NBER08/StartrackerOrion-Hardware/HTML/images/cat_pdf_drill_map_Orion-NPTH_drill_map.png

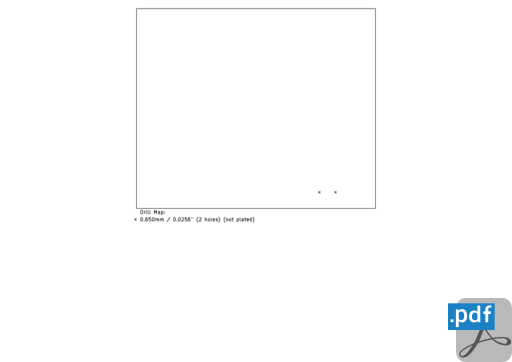
HTML/images/cat_pdf_drill_map_Orion-NPTH_drill_map.png
