NBER08/StartrackerOrion-Hardware/HTML/images/cat_pdf_drill_map_Orion-PTH_drill_map.png

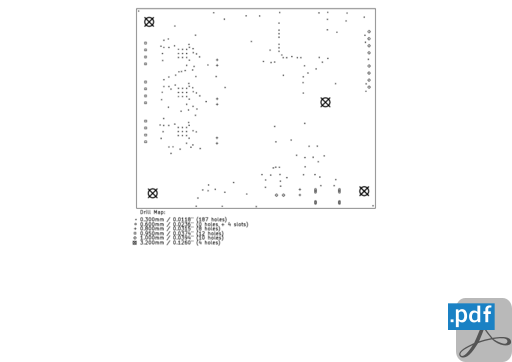
HTML/images/cat_pdf_drill_map_Orion-PTH_drill_map.png
