NBER08/StartrackerOrion-Hardware/HTML/images/cat_png_3d_viewer_bottom_Orion-bottom.png

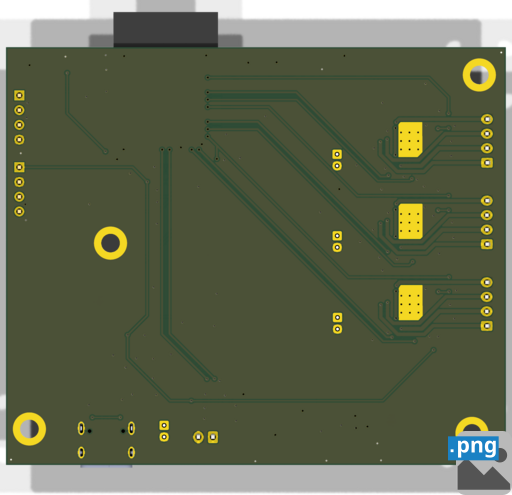
HTML/images/cat_png_3d_viewer_bottom_Orion-bottom.png
