NBER08/StartrackerOrion-Hardware/HTML/images/cat_png_3d_viewer_top_Orion-top.png

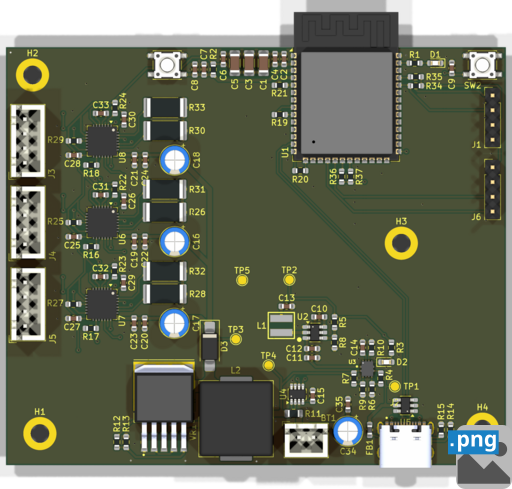
HTML/images/cat_png_3d_viewer_top_Orion-top.png
