NBER08/StartrackerOrion-Hardware/Images/Orion-bottom.png

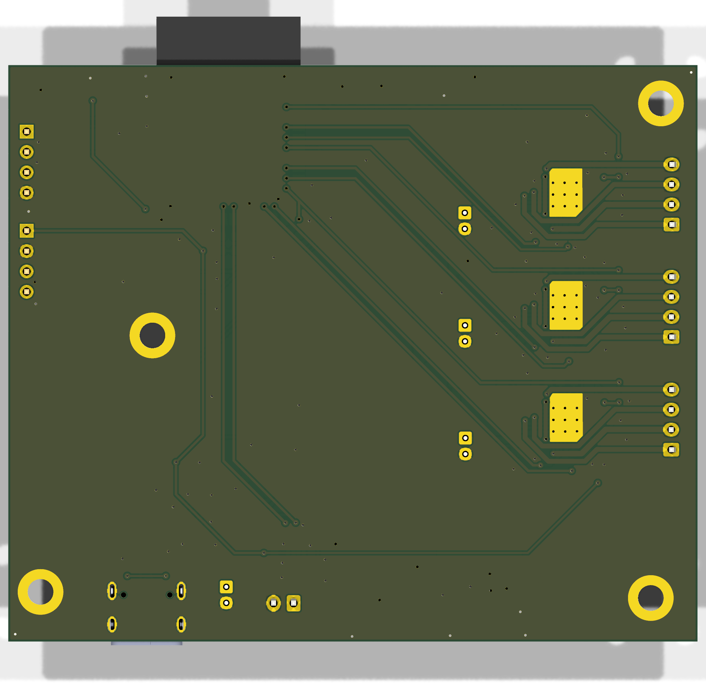
Images/Orion-bottom.png
