NBER08/StartrackerOrion-Hardware/Manufacturing/Fabrication/Orion-fabrication.pdf

# Top Fabrication (Scale 1:1)

# Orion Main Fabrication Document

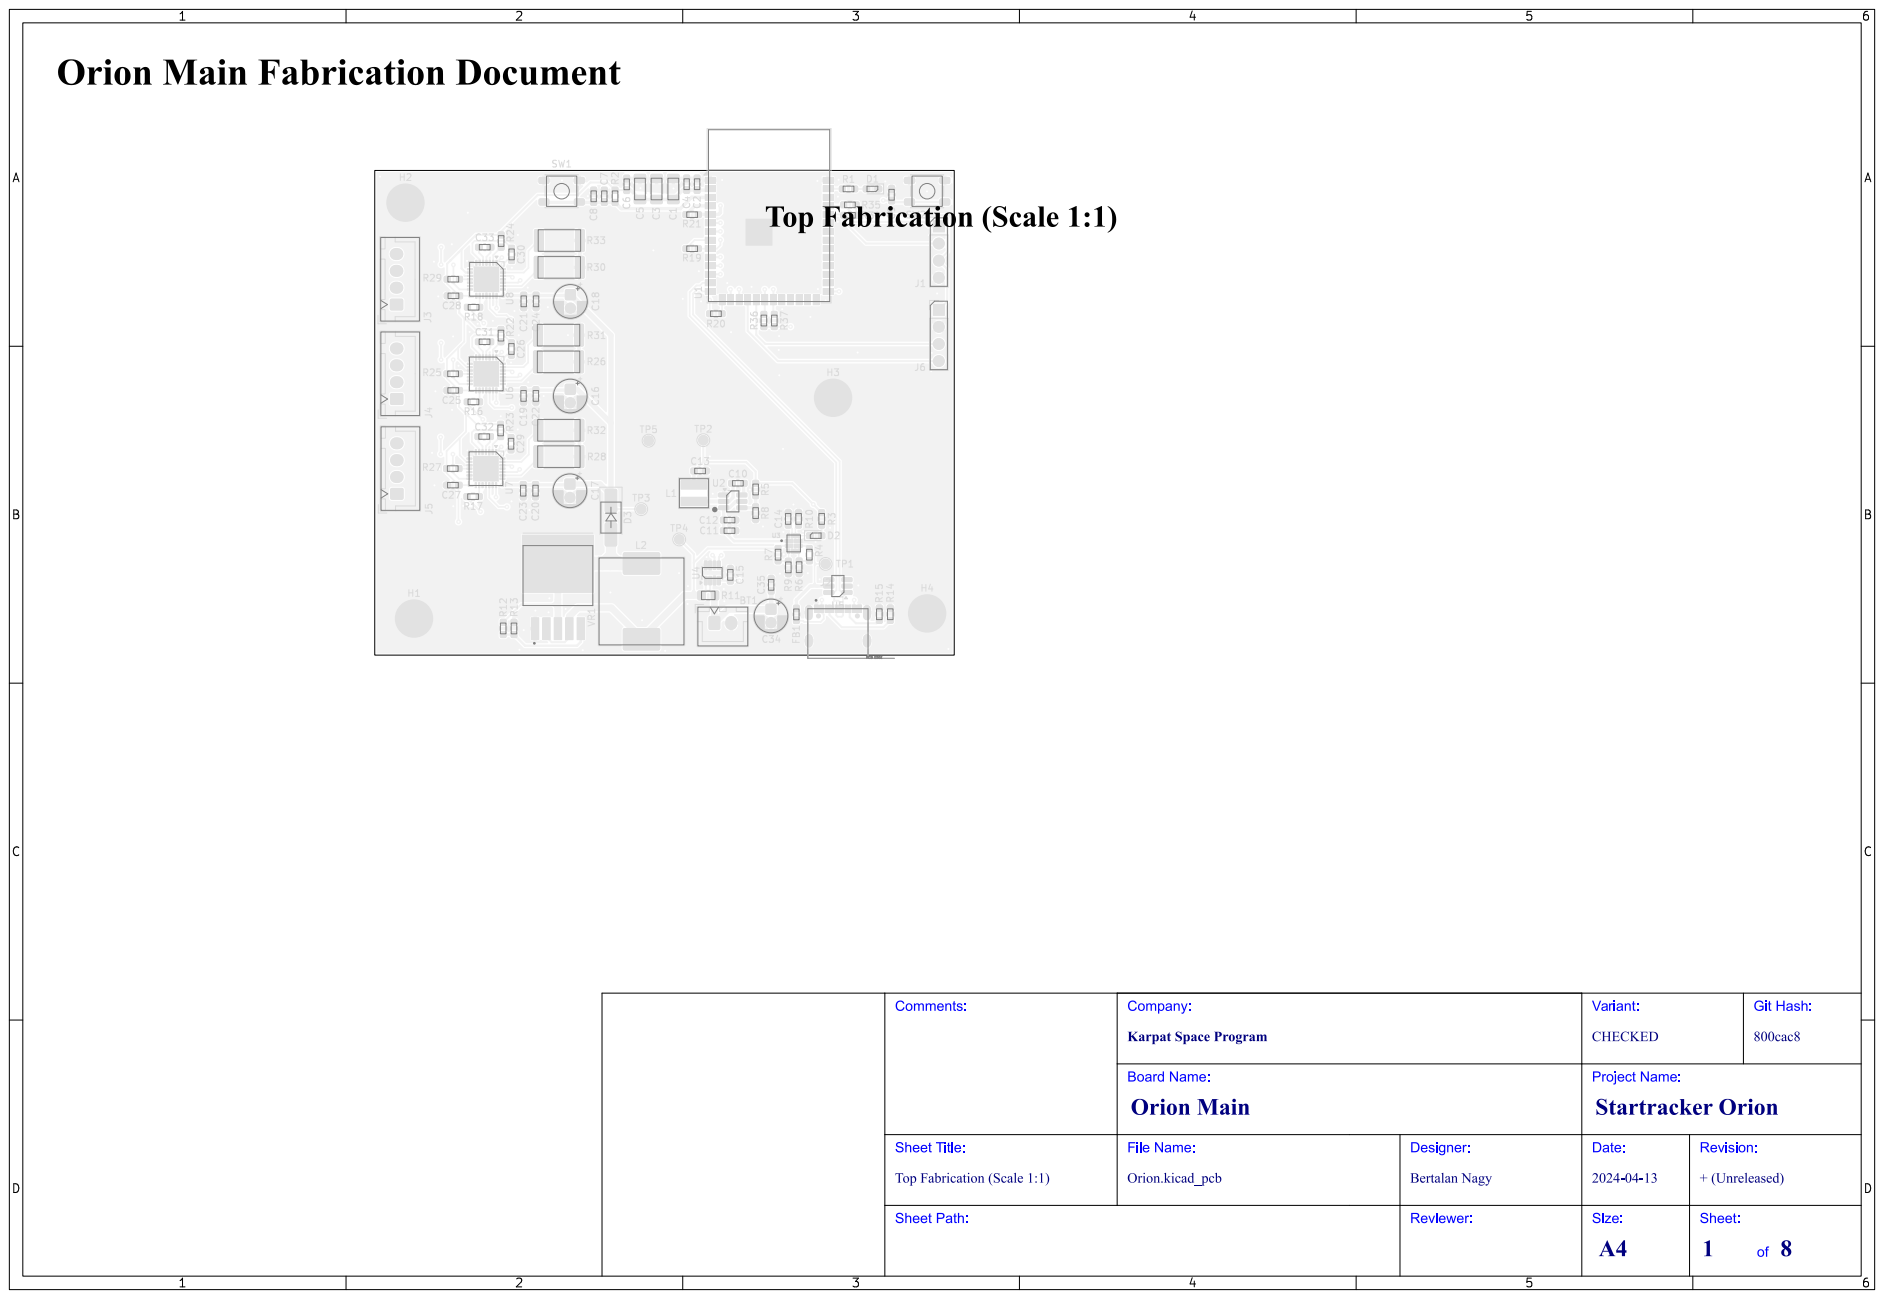
[picture p10: page 1]

# Bottom Fabrication (Scale 1:1)

# Orion Main Fabrication Document

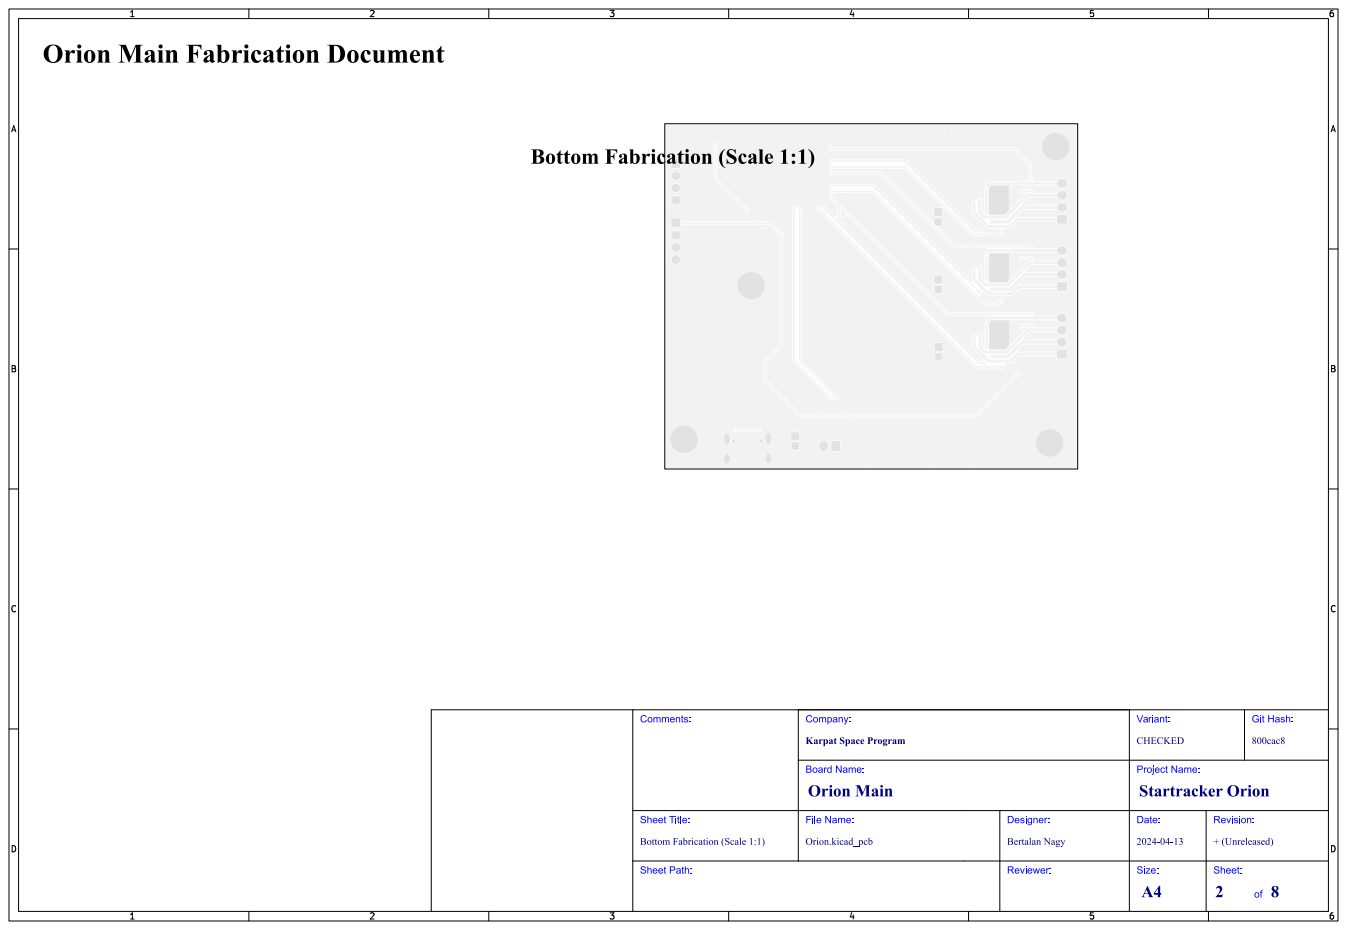
[picture p11: page 2]
Git; Hash:; 800cac8; Comments:; Sheet Path:; Sheet Title:; File Name:; Orion Main; Startracker Orion; Company:; CHECKED; Variant:; Board Name:; Orion.kicad_pcb; Bertalan Nagy; Designer:; Reviewer:; Project Name:; Date:; + (Unreleased); Revision:; Size:; Sheet:

Karpat Space Program

Bottom Fabrication (Scale 1:1)

# Drill Drawing L1 - L2 (Scale 1:1)

# Orion Main Fabrication Document

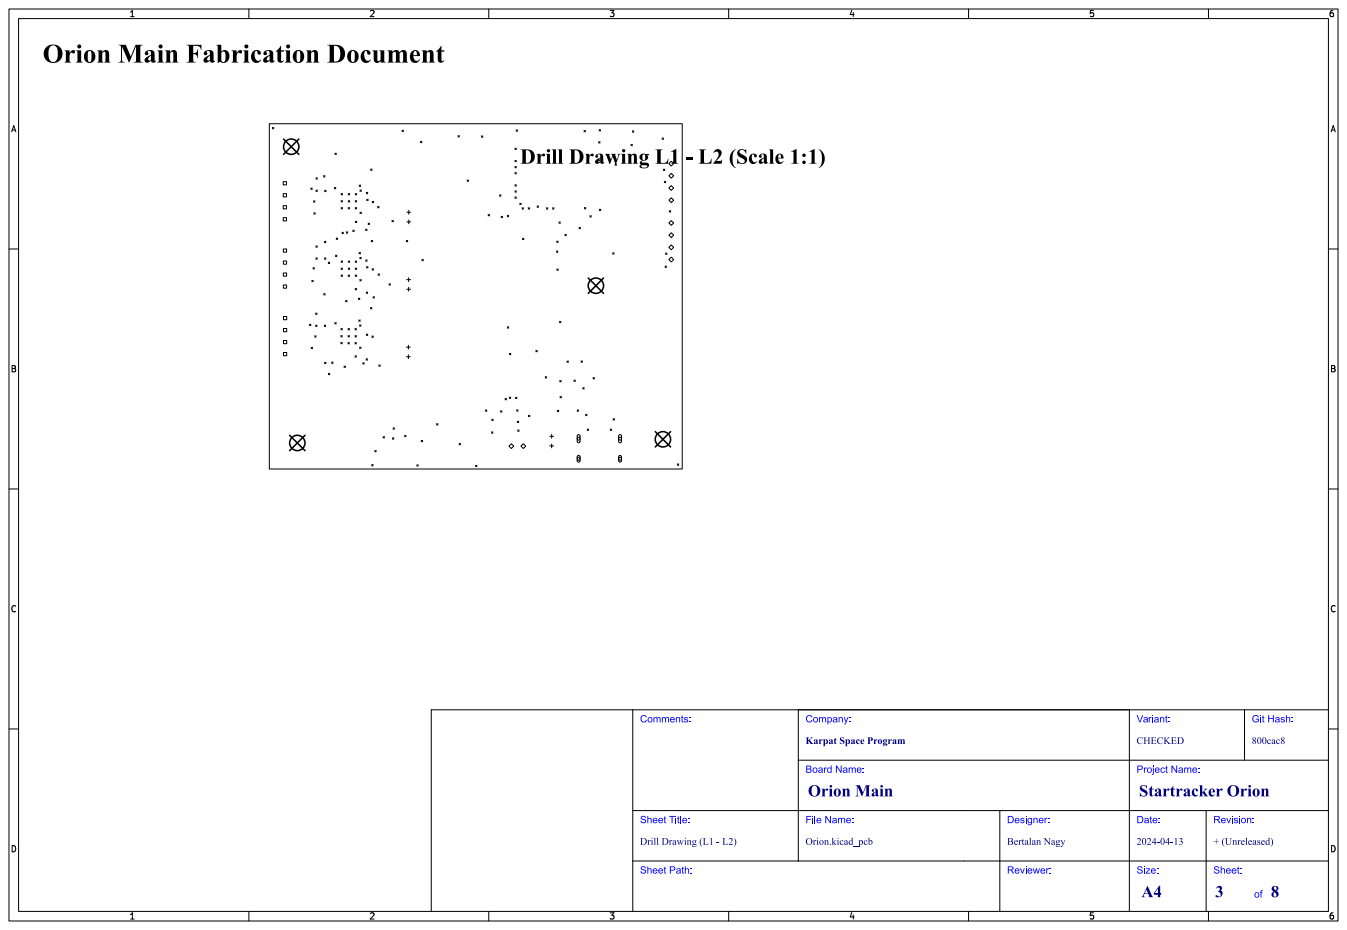
[picture p12: page 3]
Git; Hash:; 800cac8; Comments:; Drill Drawing (L1 - L2); Sheet Path:; Sheet Title:; File Name:; Orion Main; Startracker Orion; Company:; CHECKED; Variant:; Board Name:; Orion.kicad_pcb; Bertalan Nagy; Designer:; Reviewer:; Project Name:; Date:; + (Unreleased); Revision:; Size:; Sheet:

Karpat Space Program

# Drill Drawing L1 - L2 (Scale 1:1)

# Orion Main Fabrication Document

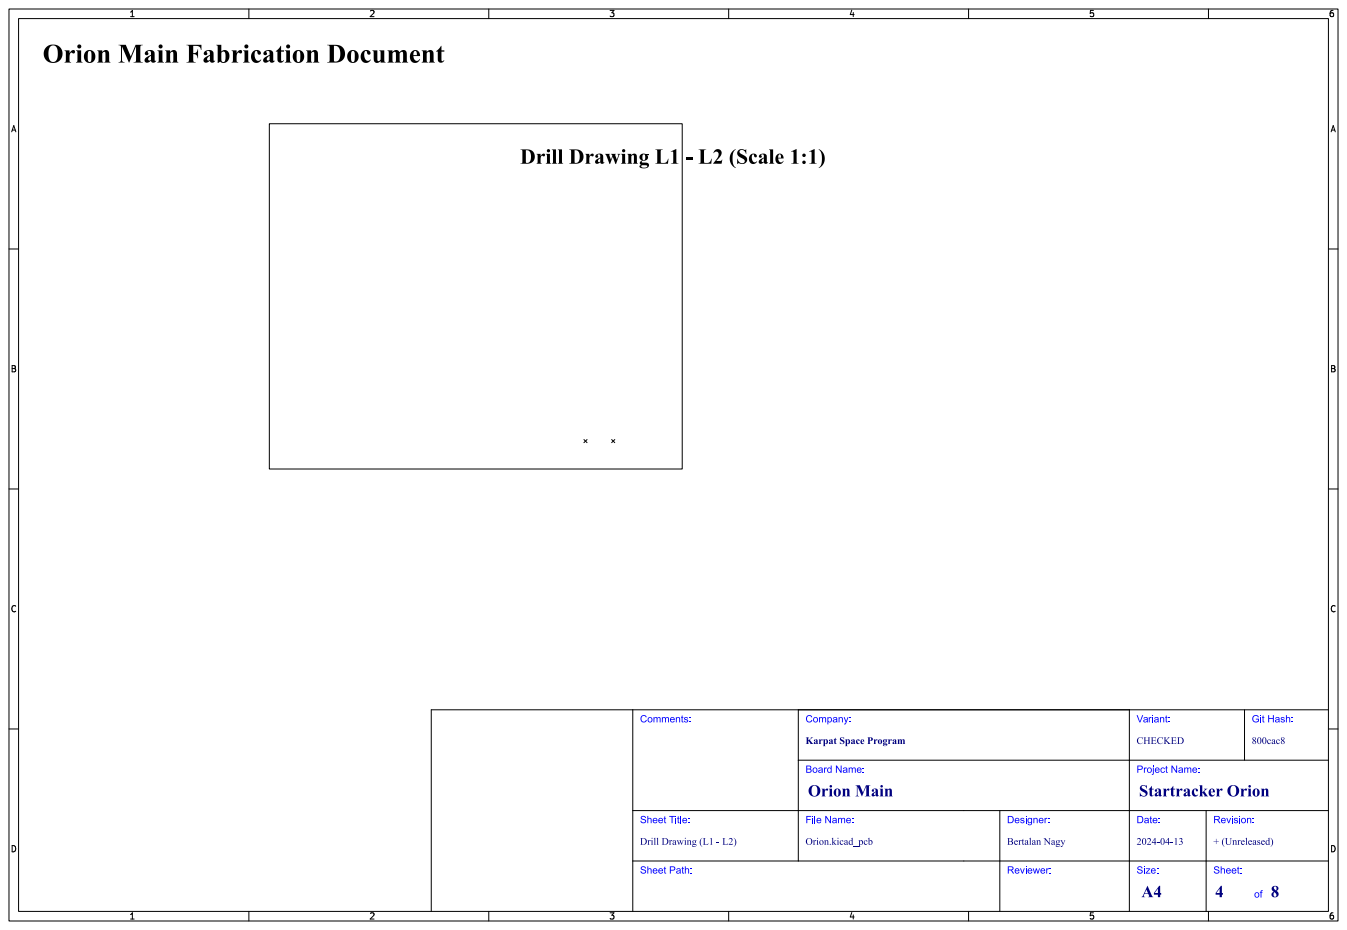
[picture p13: page 4]
Git; Hash:; 800cac8; Comments:; Drill Drawing (L1 - L2); Sheet Path:; Sheet Title:; File Name:; Orion Main; Startracker Orion; Company:; CHECKED; Variant:; Board Name:; Orion.kicad_pcb; Bertalan Nagy; Designer:; Reviewer:; Project Name:; Date:; + (Unreleased); Revision:; Size:; Sheet:

Karpat Space Program

# Top Test Points (Scale 1:1)

# Orion Main Fabrication Document

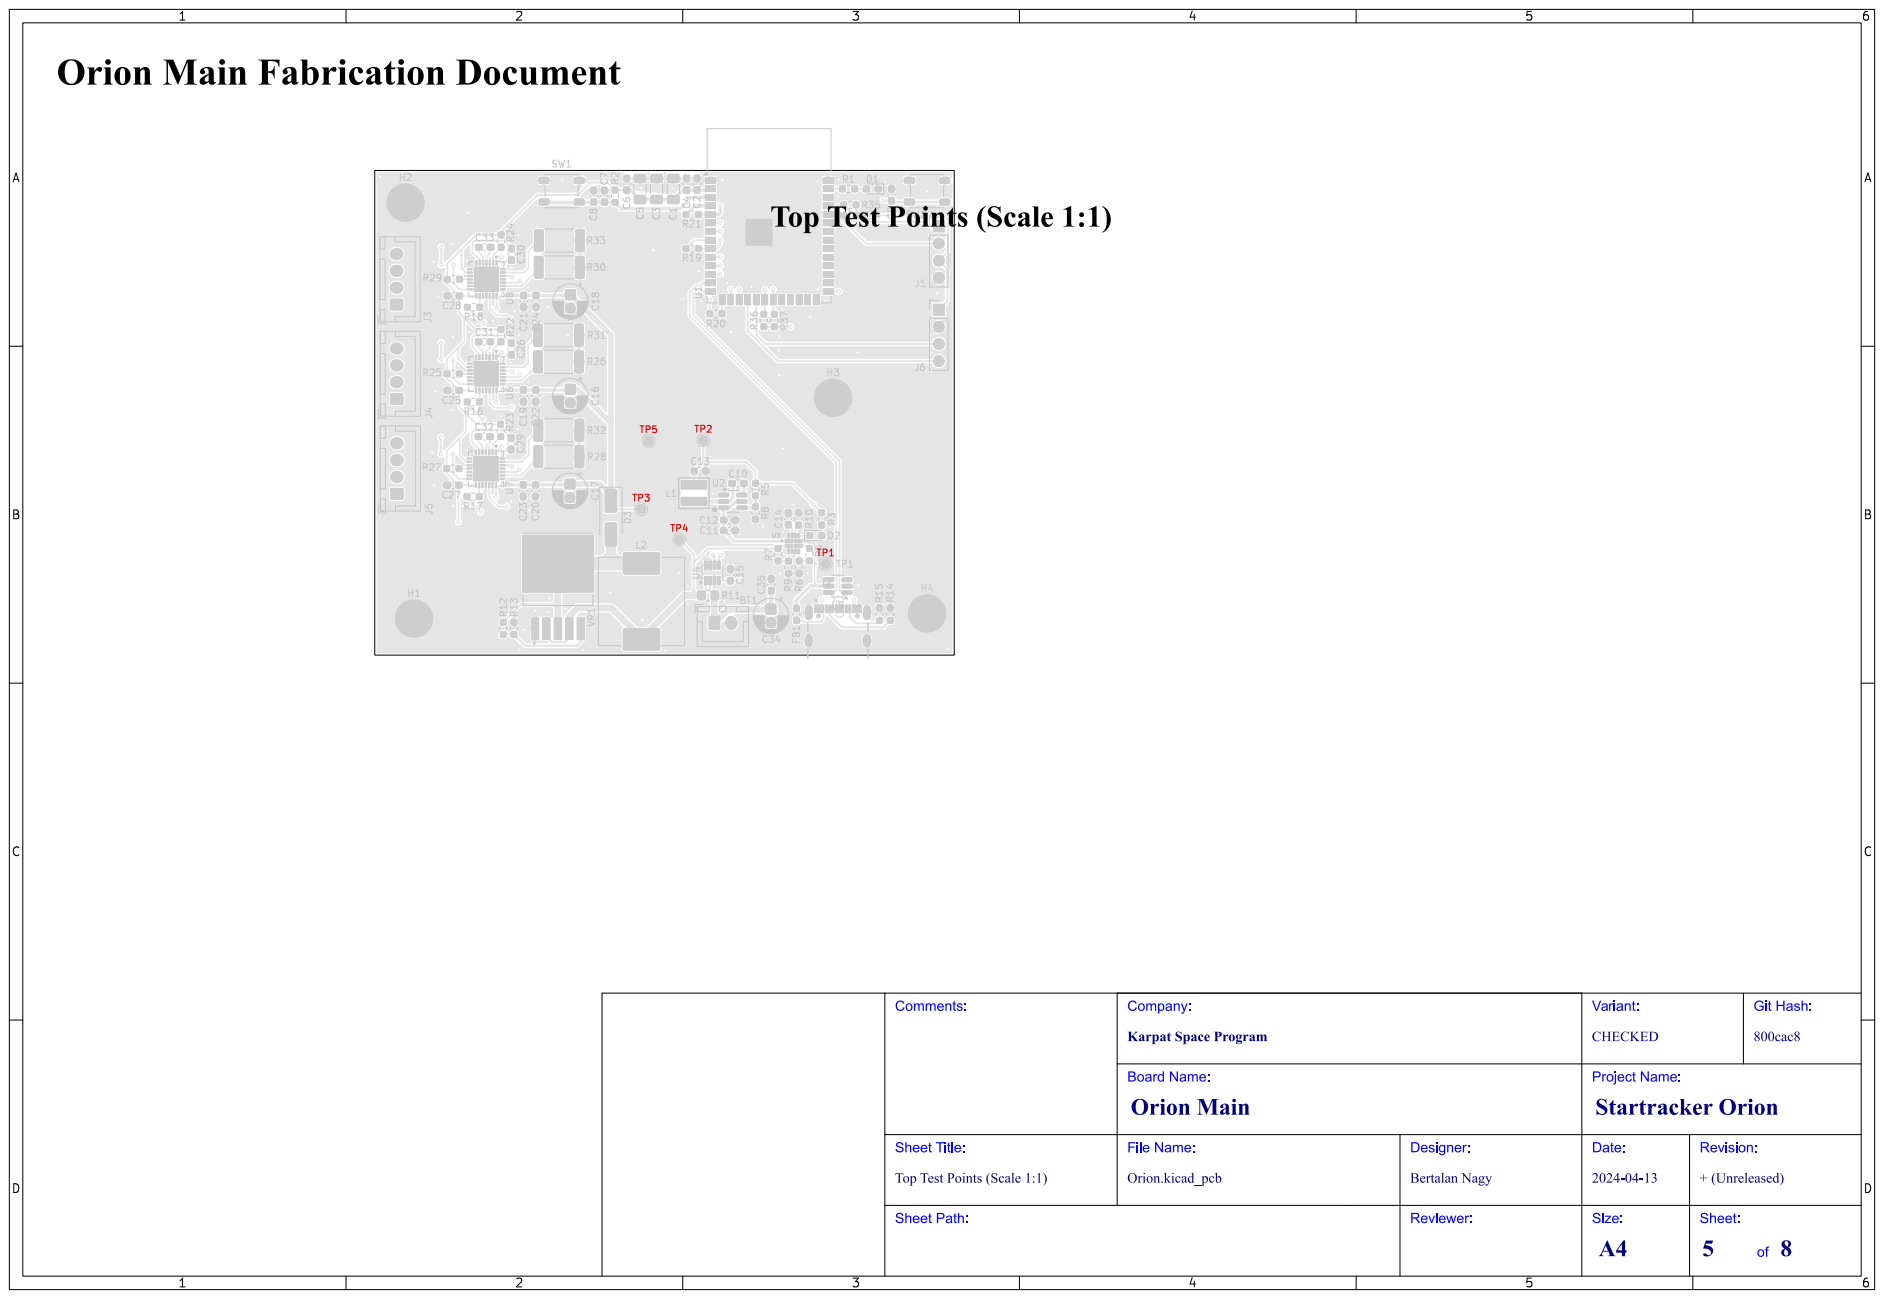
[picture p14: page 5]

Top Test Points (Scale 1:1)

# Bottom Test Points (Scale 1:1)

# Orion Main Fabrication Document

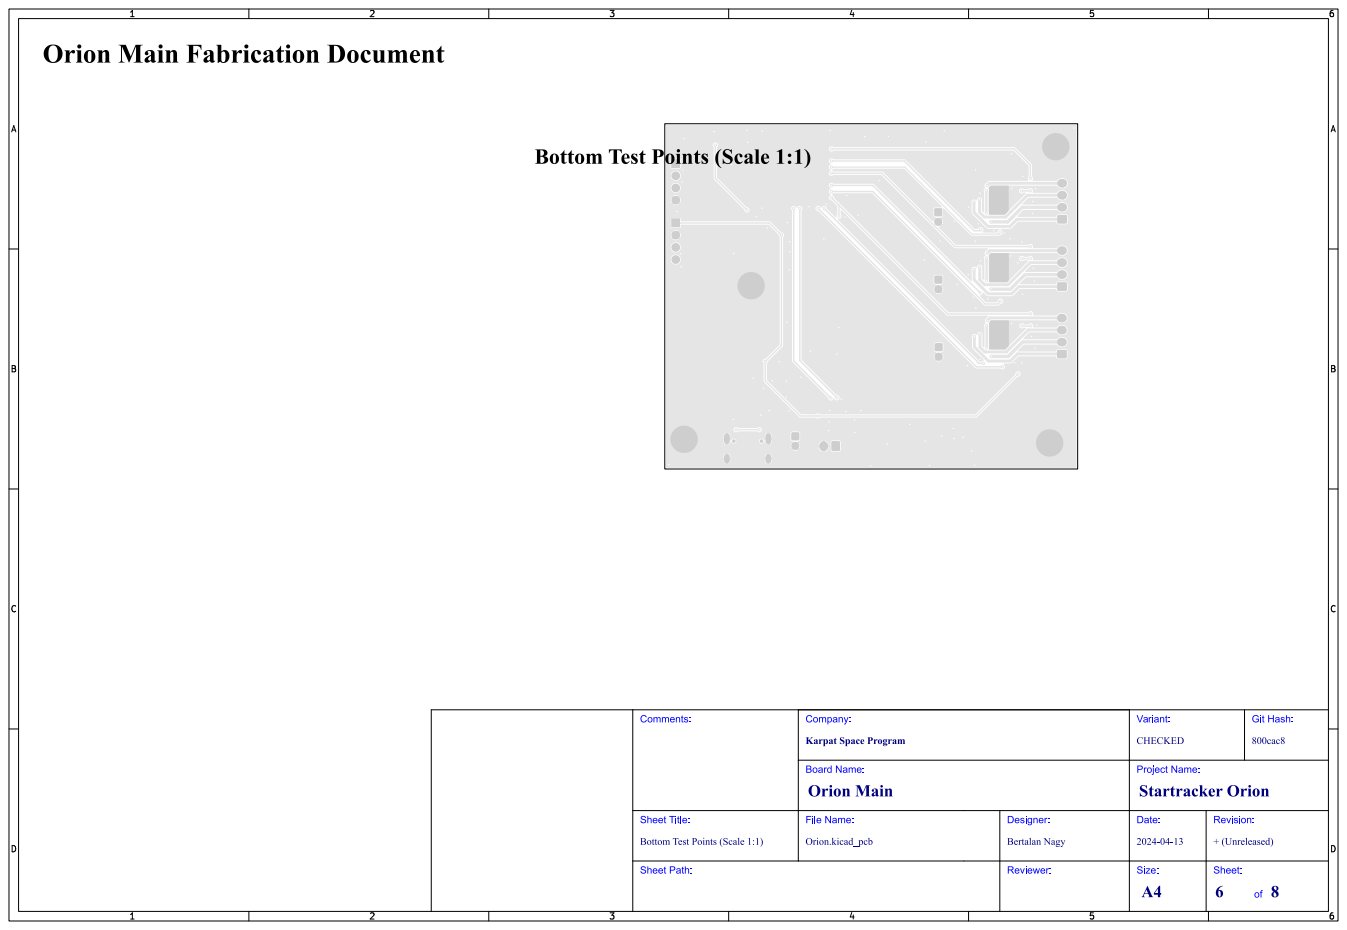
[picture p15: page 6]
Git; Hash:; 800cac8; Comments:; Sheet Path:; Sheet Title:; File Name:; Orion Main; Startracker Orion; Company:; CHECKED; Variant:; Board Name:; Orion.kicad_pcb; Bertalan Nagy; Designer:; Reviewer:; Project Name:; Date:; + (Unreleased); Revision:; Size:; Sheet:

Karpat Space Program

Bottom Test Points (Scale 1:1)

# L1 (Sig, PWR) (Scale 1:1)

# Orion Main Fabrication Document

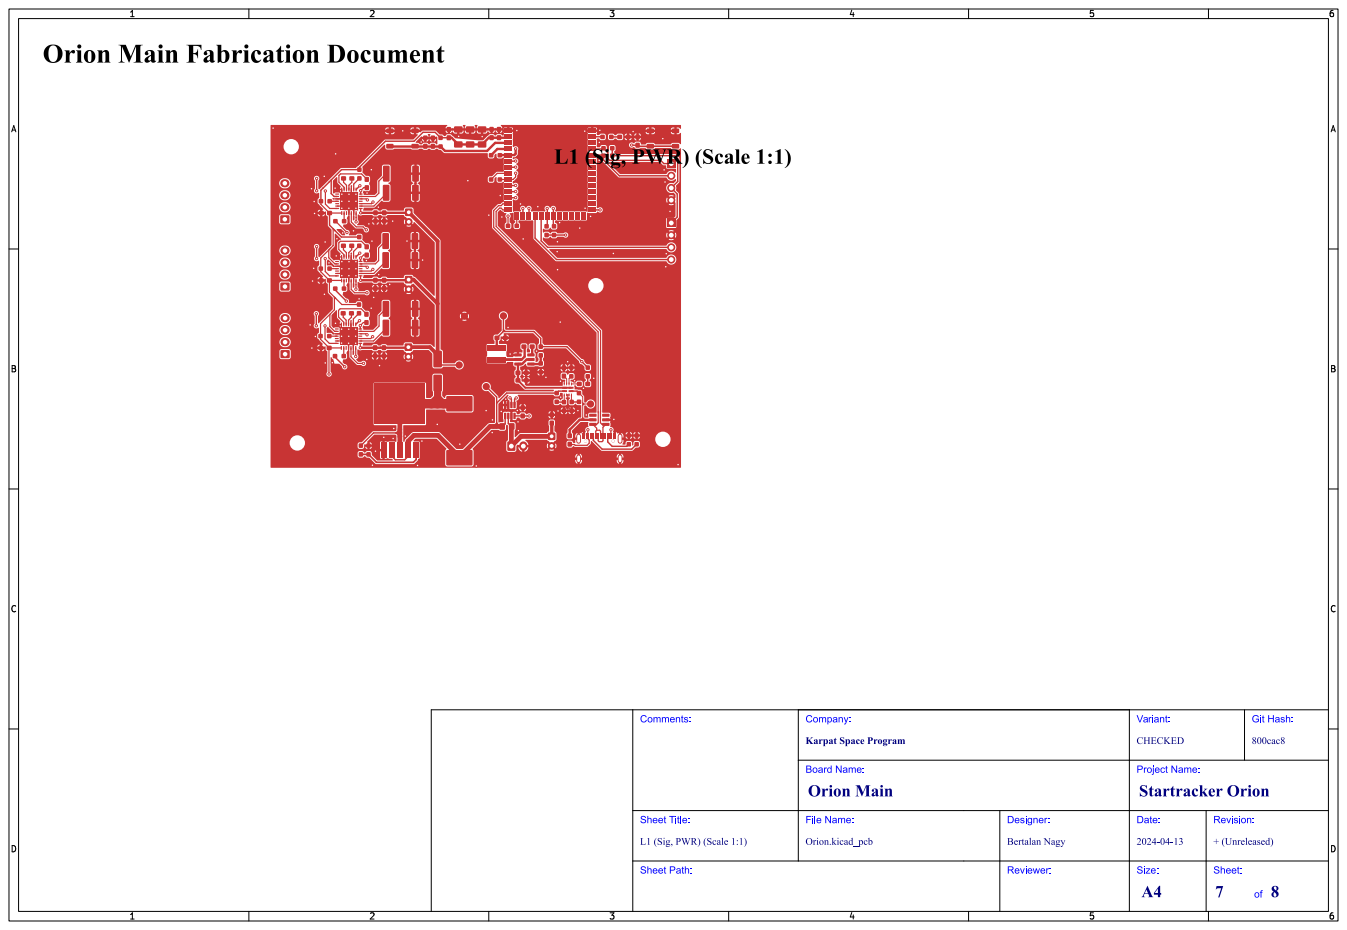
[picture p16: page 7]
Git; Hash:; 800cac8; Comments:; Sheet Path:; Sheet Title:; File Name:; Orion Main; Startracker Orion; Company:; CHECKED; Variant:; Board Name:; Orion.kicad_pcb; Bertalan Nagy; Designer:; Reviewer:; Project Name:; Date:; + (Unreleased); Revision:; Size:; Sheet:

Karpat Space Program

L1 (Sig, PWR) (Scale 1:1)

# L4 (Sig, PWR) (Scale 1:1)

# Orion Main Fabrication Document

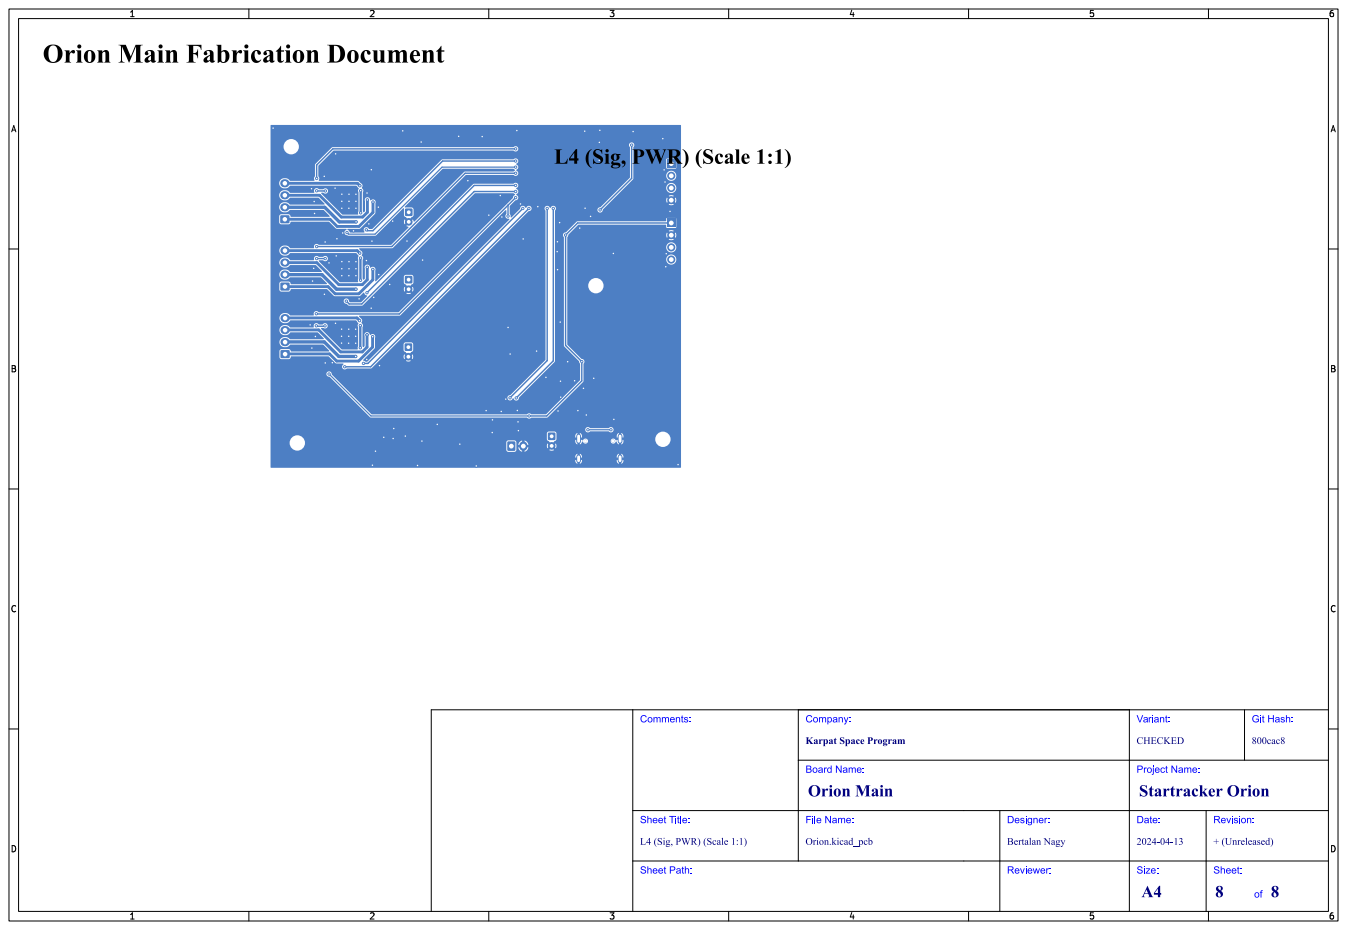
[picture p17: page 8]
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

Karpat Space Program

L4 (Sig, PWR) (Scale 1:1)
