NBER08/StartrackerOrion-Hardware/Manufacturing/Fabrication/Gerbers/Orion-NPTH_drill_map.pdf

Drill Map:
0.650mm / 0.0256" (2 holes) (not plated)
