NBER08/StartrackerOrion-Hardware/Manufacturing/Fabrication/Orion-fabrication-10.pdf

# L4 (Sig, PWR) (Scale 1:1)

# Orion Main Fabrication Document

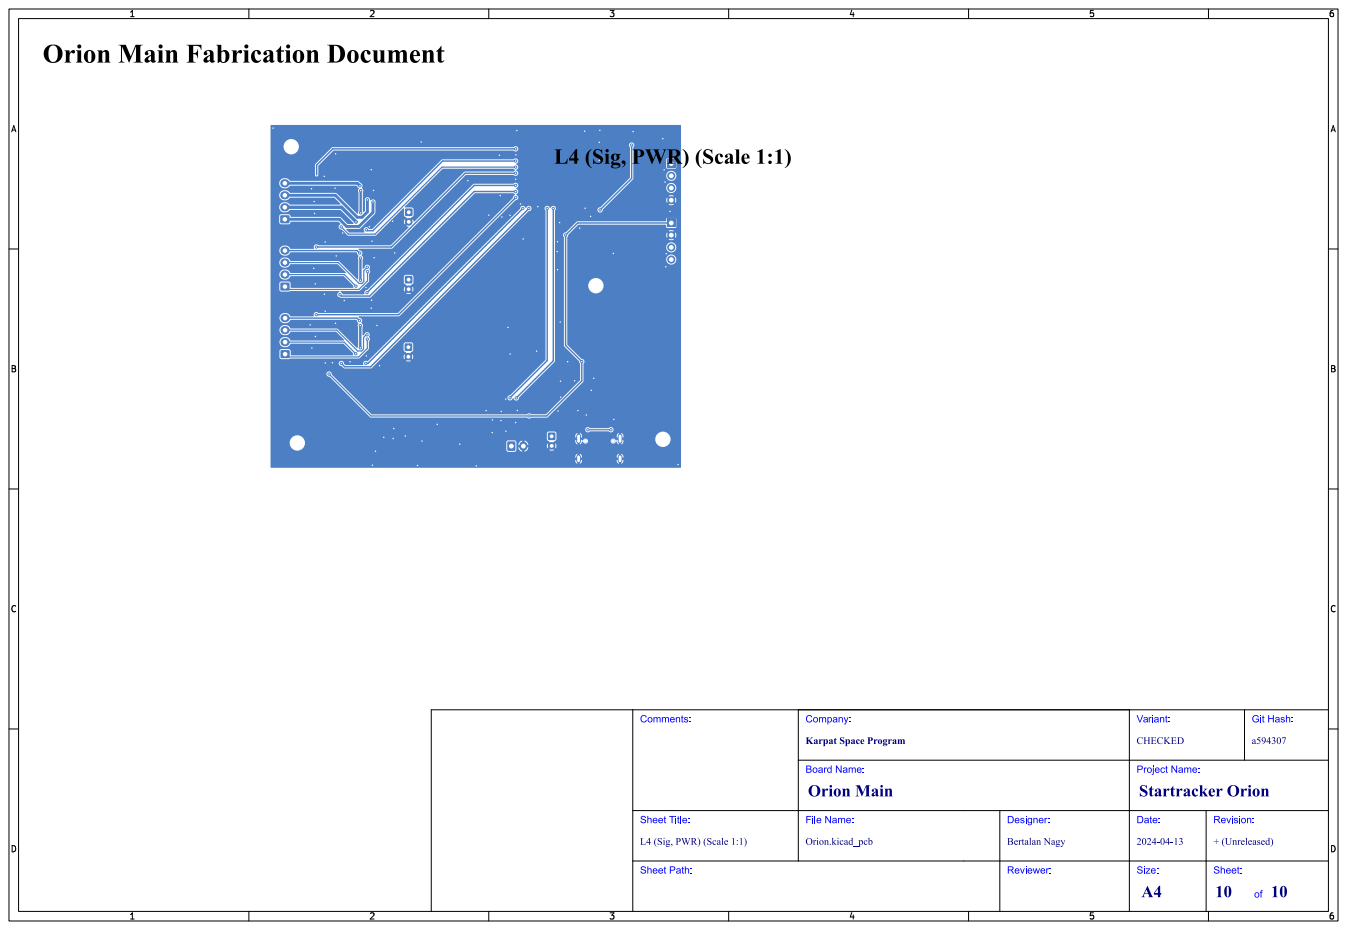
[picture p29: page 1]
Git; Hash:; Comments:; Sheet Path:; Sheet Title:; File Name:; Orion Main; Startracker Orion; Company:; CHECKED; Variant:; Board Name:; Orion.kicad_pcb; Bertalan Nagy; Designer:; Reviewer:; Project Name:; Date:; + (Unreleased); Revision:; Size:; Sheet: 10

Karpat Space Program

L4 (Sig, PWR) (Scale 1:1)
