NBER08/StartrackerOrion-Hardware/Manufacturing/Fabrication/Orion-fabrication-2.pdf

# Bottom Fabrication (Scale 1:1)

# Orion Main Fabrication Document

Git; Hash:; 800cac8; Comments:; Sheet Path:; Sheet Title:; File Name:; Orion Main; Startracker Orion; Company:; CHECKED; Variant:; Board Name:; Orion.kicad_pcb; Bertalan Nagy; Designer:; Reviewer:; Project Name:; Date:; + (Unreleased); Revision:; Size:; Sheet: 2

Karpat Space Program

Bottom Fabrication (Scale 1:1)
