NBER08/StartrackerOrion-Hardware/Manufacturing/Fabrication/Orion-fabrication-9.pdf

# L3 (GND) (Scale 1:1)

# Orion Main Fabrication Document

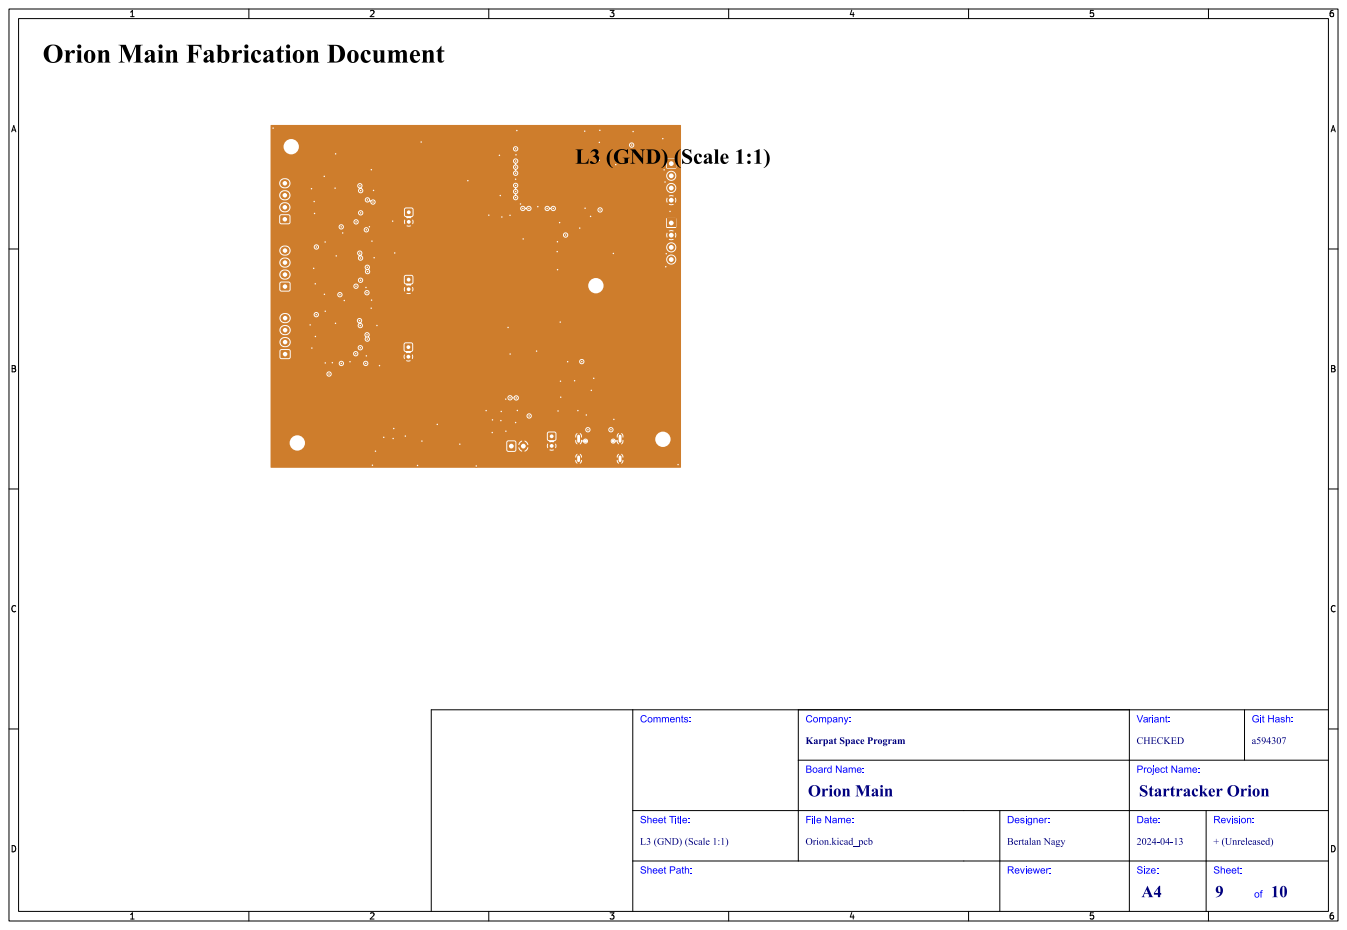
[picture p30: page 1]
Git; Hash:; Comments:; L3 (GND) (Scale 1:1); Sheet Path:; Sheet Title:; File Name:; Orion Main; Startracker Orion; Company:; CHECKED; Variant:; Board Name:; Orion.kicad_pcb; Bertalan Nagy; Designer:; Reviewer:; Project Name:; Date:; + (Unreleased); Revision:; Size:; Sheet: 9

Karpat Space Program
