NBER08/StartrackerOrion-Hardware/Manufacturing/Fabrication/Orion-fabrication-1.pdf

# Top Fabrication (Scale 1:1)

# Orion Main Fabrication Document
