NBER08/StartrackerOrion-Hardware/Manufacturing/Fabrication/Orion-fabrication-5.pdf

# Top Test Points (Scale 1:1)

# Orion Main Fabrication Document


Top Test Points (Scale 1:1)
