NBER08/StartrackerOrion-Hardware/Manufacturing/Fabrication/Gerbers/Orion-PTH_drill_map.pdf

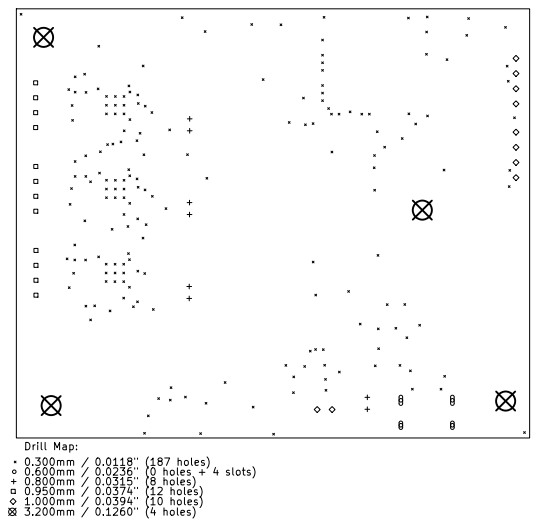
[picture p31: page 1]
